lewispg228/audioflyer/arduino_sketches/4_on_the_floor/track_numbers.h

// WAVE File number defines
// (these match up with the actual WAV file names on the uSD card)
#define KICK 100
#define SNARE 101
#define HAT 102
#define RIDE 103

// set default tracks assigned to actively used kick/snare/hat/etc. varialbles
// variables used for playback in main program
int kick_t = KICK;
int snare_t = SNARE;
int hat_t = HAT;
int ride_t = RIDE;
